rdtrob/rdt_manet_enclosure/images/2.jpg

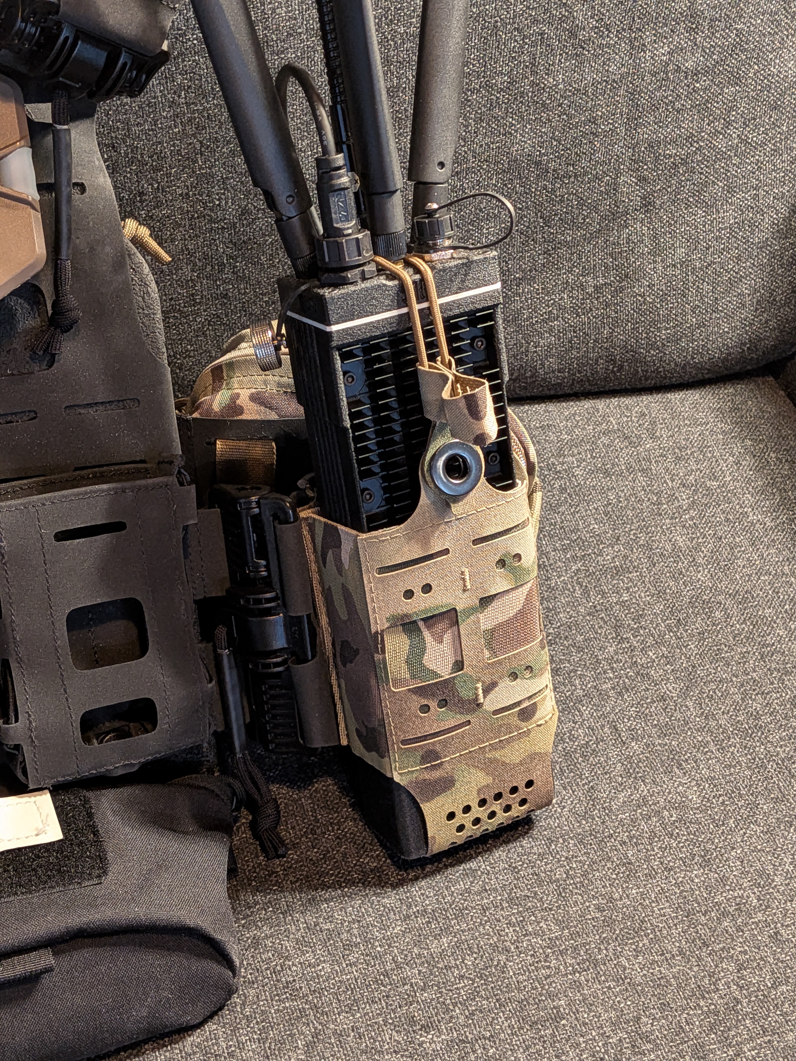
images/2.jpg
