rdtrob/rdt_manet_enclosure/images/3.jpg

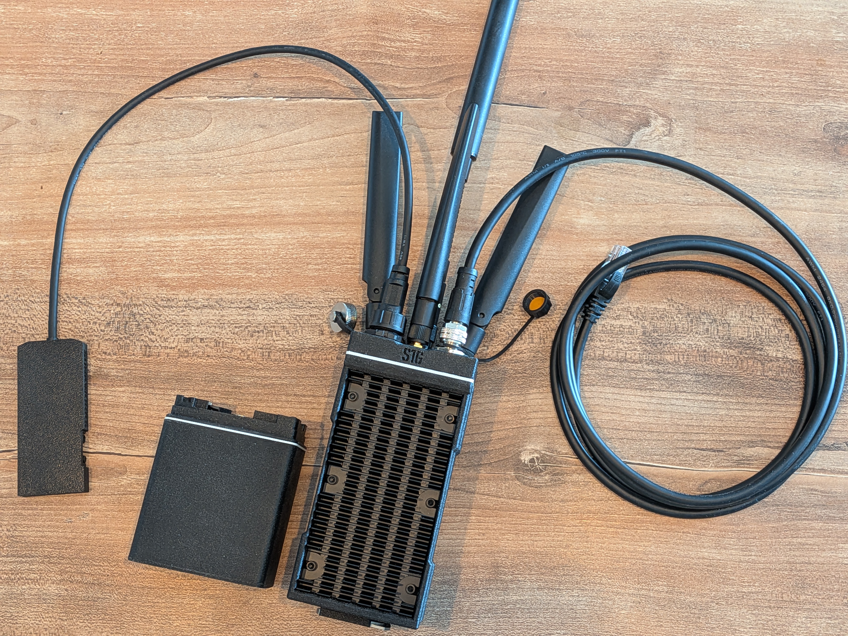
images/3.jpg
