rdtrob/rdt_manet_enclosure/images/5.jpg

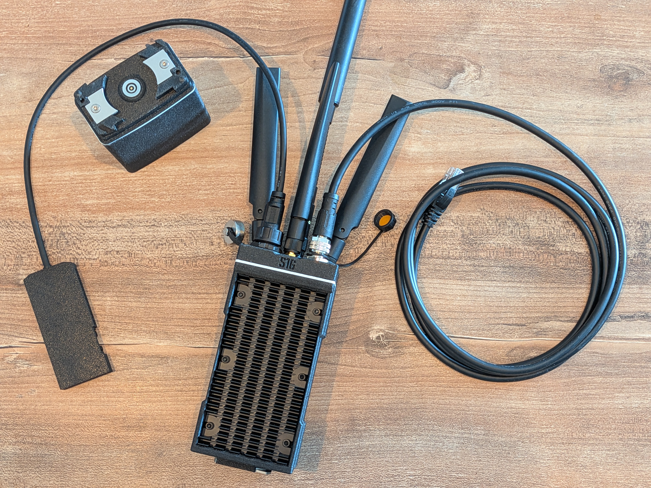
images/5.jpg
