rdtrob/rdt_manet_enclosure/images/6.jpg

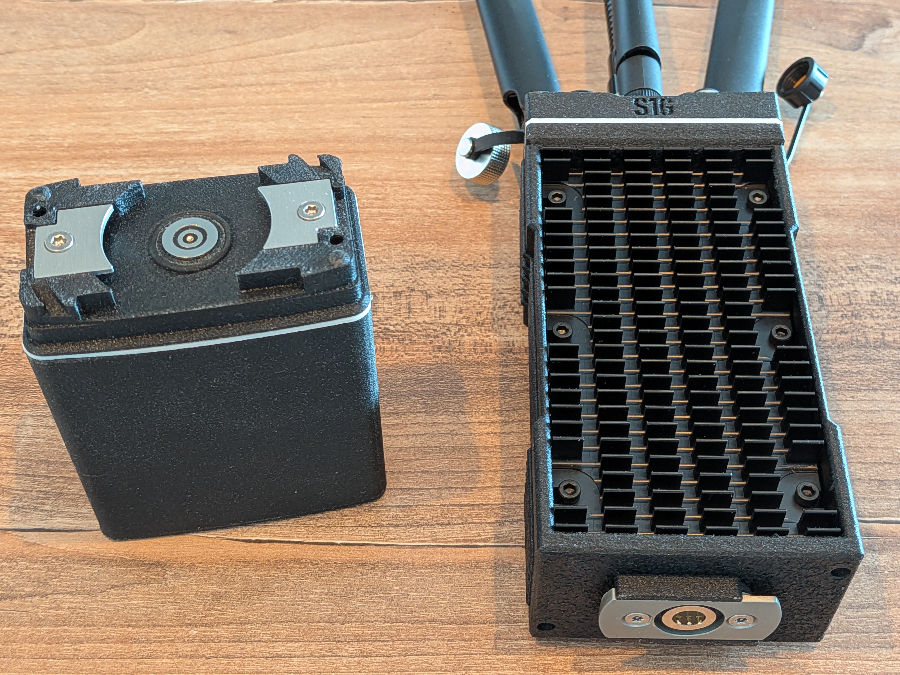
images/6.jpg
