rdtrob/rdt_manet_enclosure/images/7.jpg

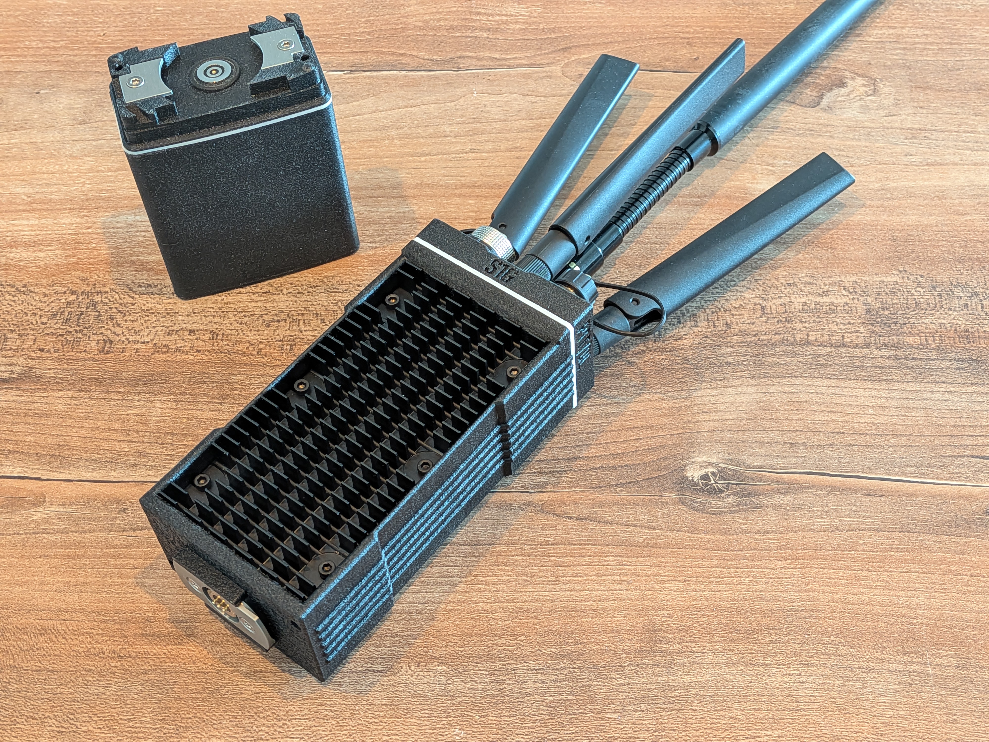
images/7.jpg
