rdtrob/rdt_manet_enclosure/images/8.jpg

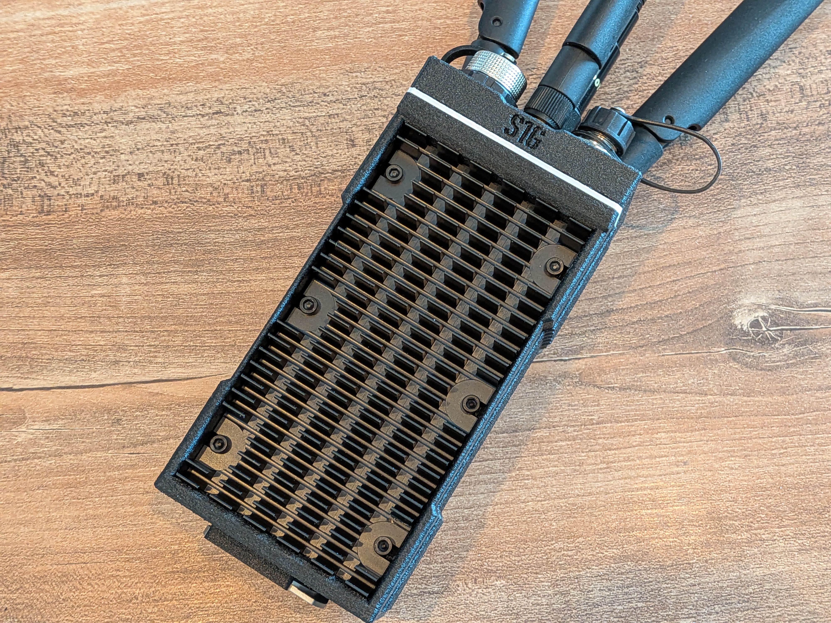
images/8.jpg
