rdtrob/rdt_manet_enclosure/images/9.jpg

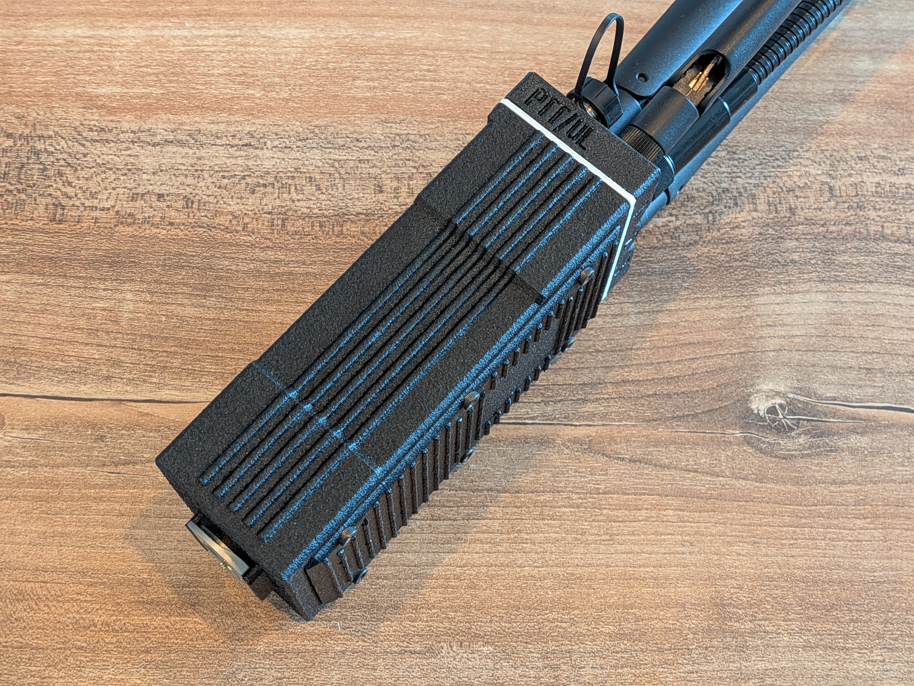
images/9.jpg
