rdtrob/rdt_manet_enclosure/images/10.jpg

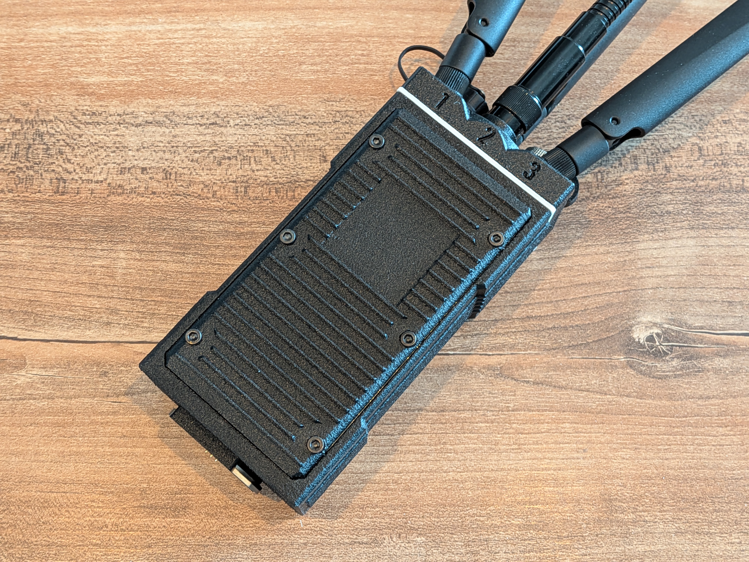
images/10.jpg
