rdtrob/rdt_manet_enclosure/images/11.jpg

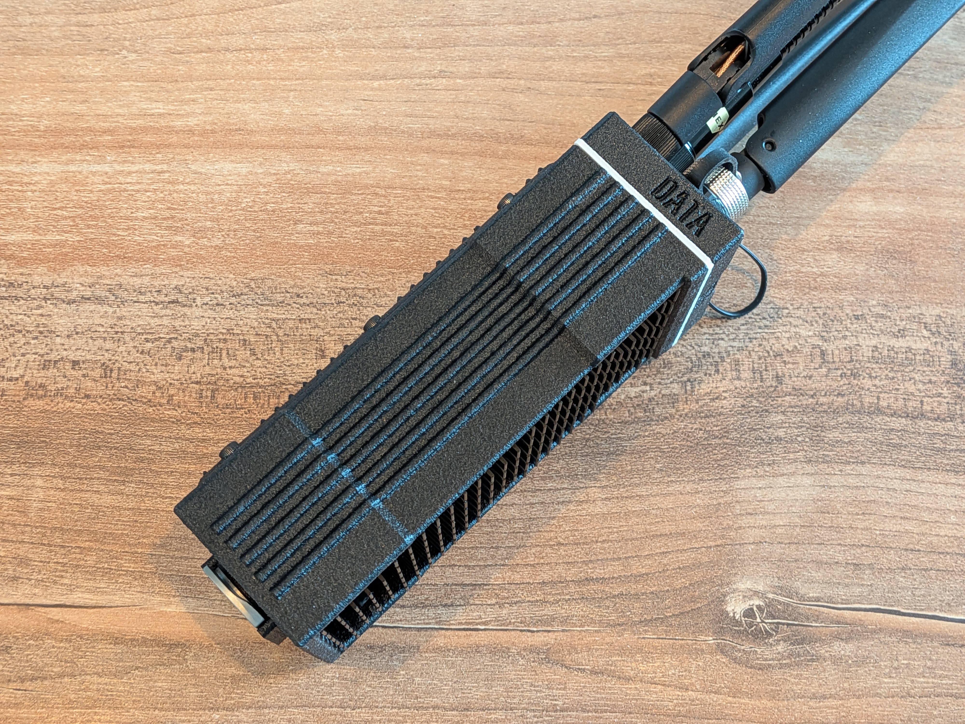
images/11.jpg
