rdtrob/rdt_manet_enclosure/images/12.jpg

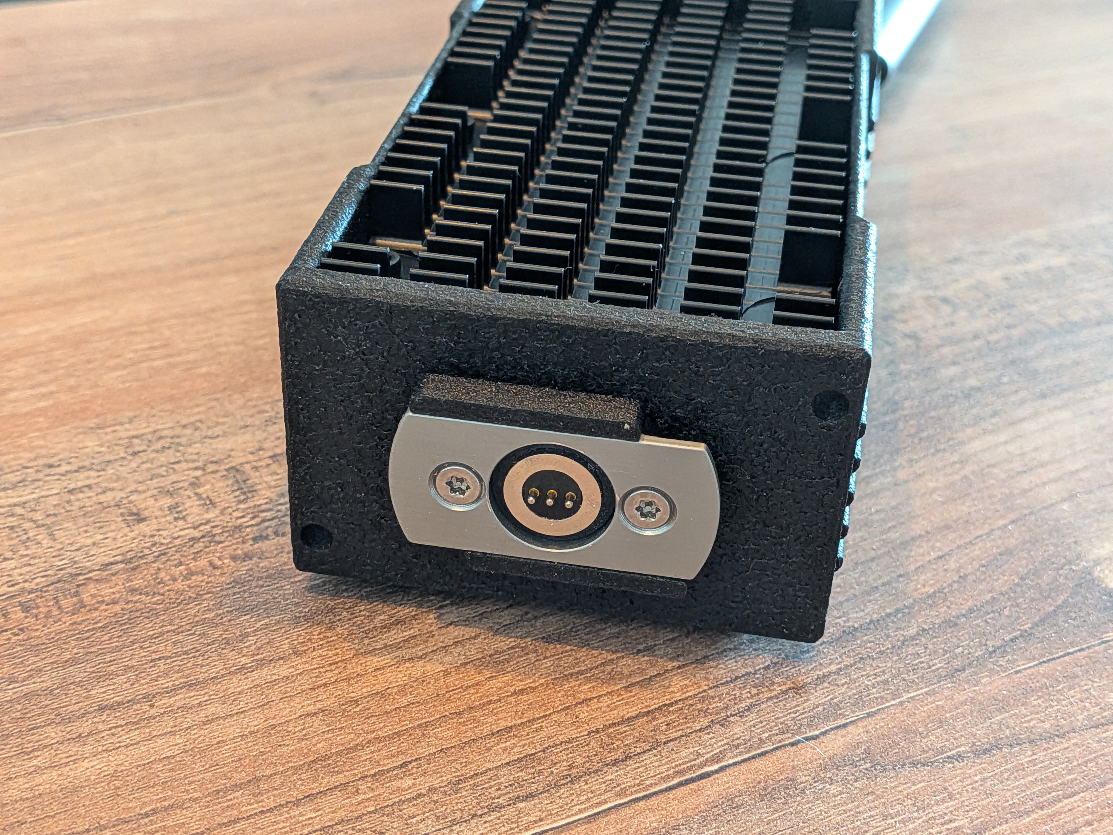
images/12.jpg
