rdtrob/rdt_manet_enclosure/images/13.jpg

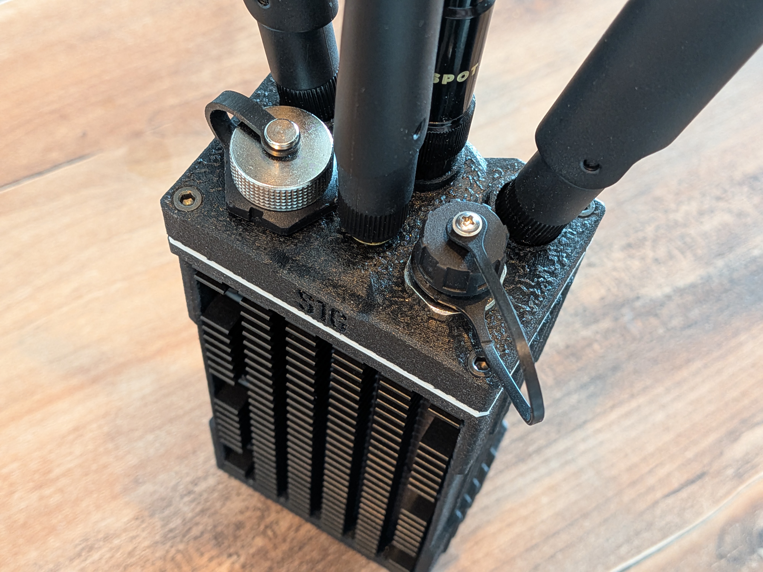
images/13.jpg
