rdtrob/rdt_manet_enclosure/images/14.jpg

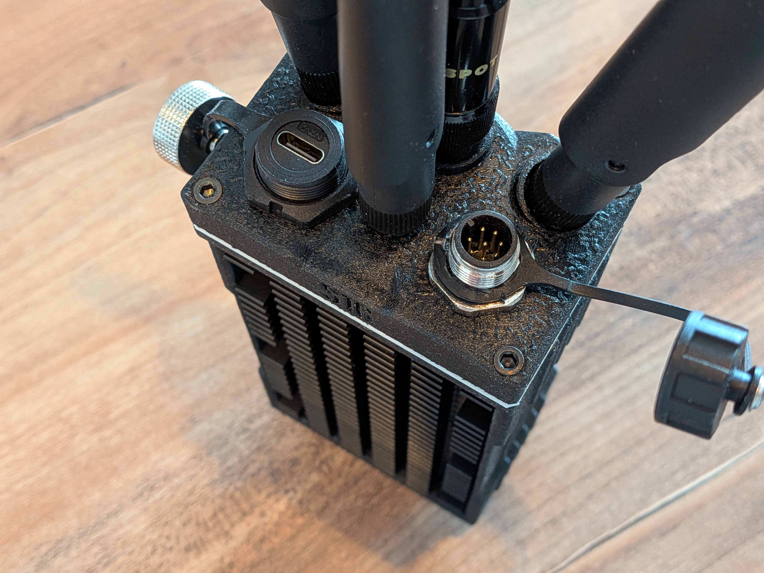
images/14.jpg
