rdtrob/rdt_manet_enclosure/images/15.jpg

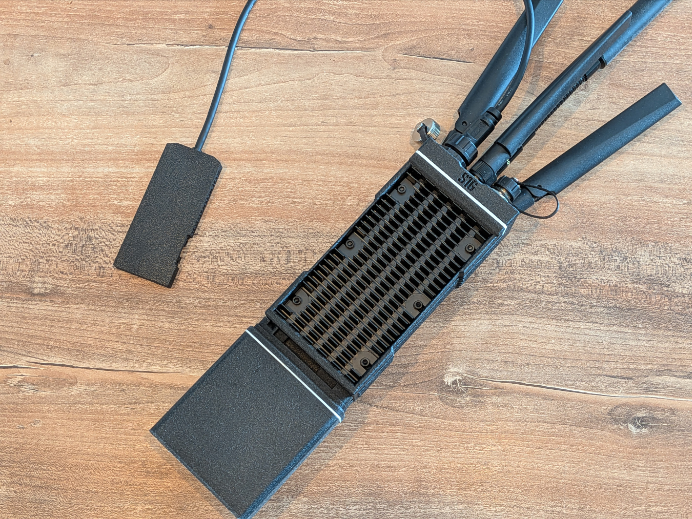
images/15.jpg
