rdtrob/rdt_manet_enclosure/images/16.jpg

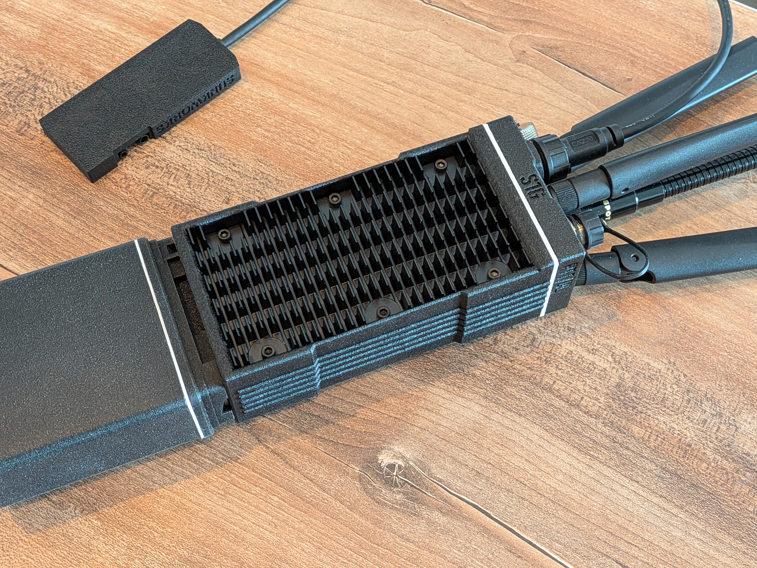
images/16.jpg
