rdtrob/rdt_manet_enclosure/images/render/render_1.png

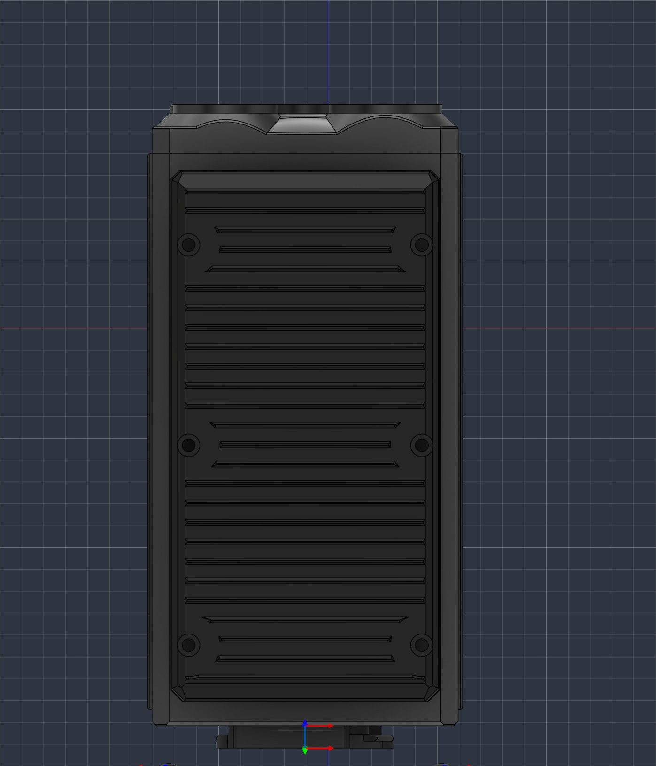
images/render/render_1.png
