rdtrob/rdt_manet_enclosure/images/render/render_2.png

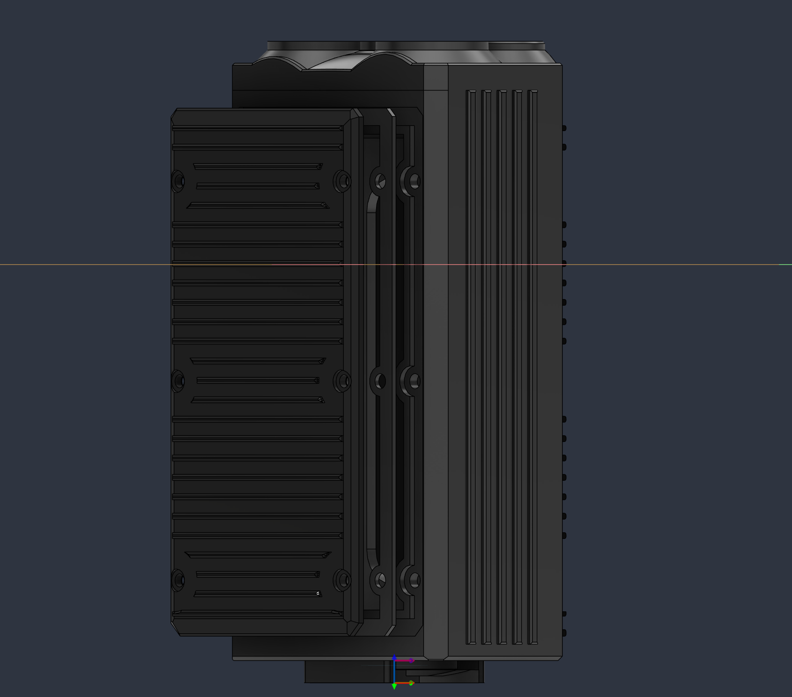
images/render/render_2.png
