rdtrob/rdt_manet_enclosure/images/render/render_3.png

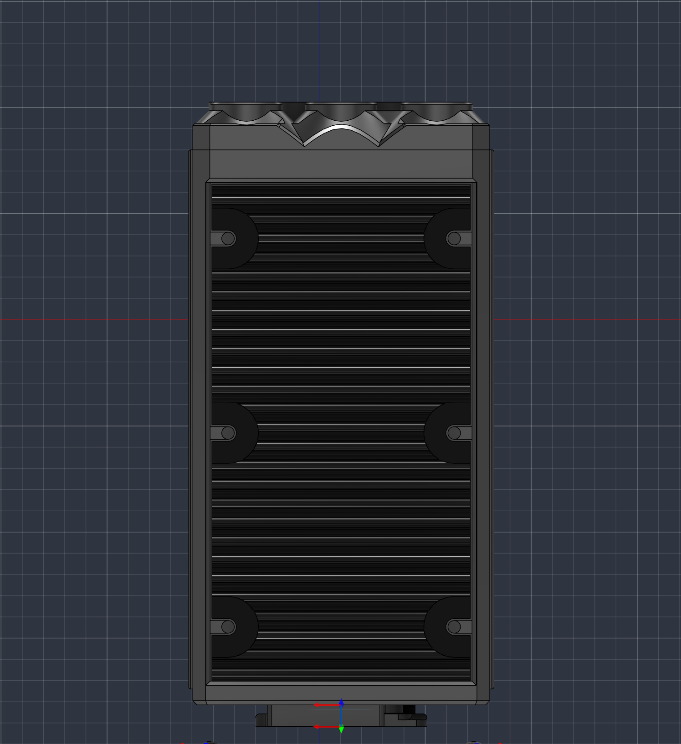
images/render/render_3.png
