rdtrob/rdt_manet_enclosure/images/render/render_5.png

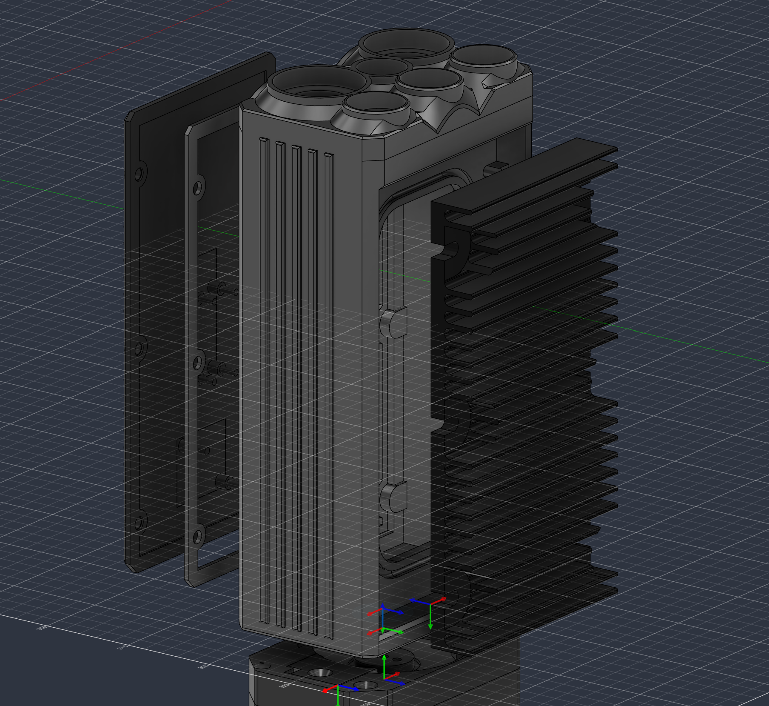
images/render/render_5.png
