rdtrob/rdt_manet_enclosure/images/components/external_USB-C_connector.png

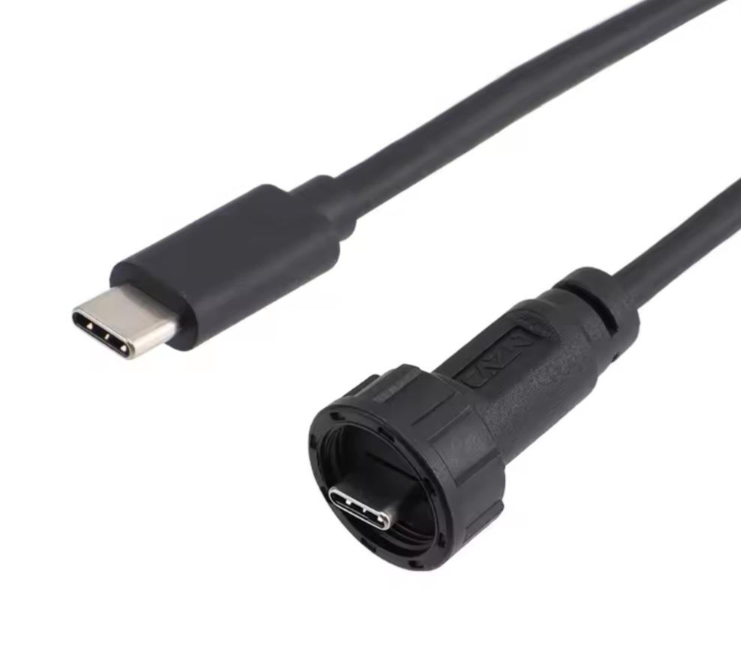
images/components/external_USB-C_connector.png
