rdtrob/rdt_manet_enclosure/images/components/flat_USB-A_to_USB-C_cable.png

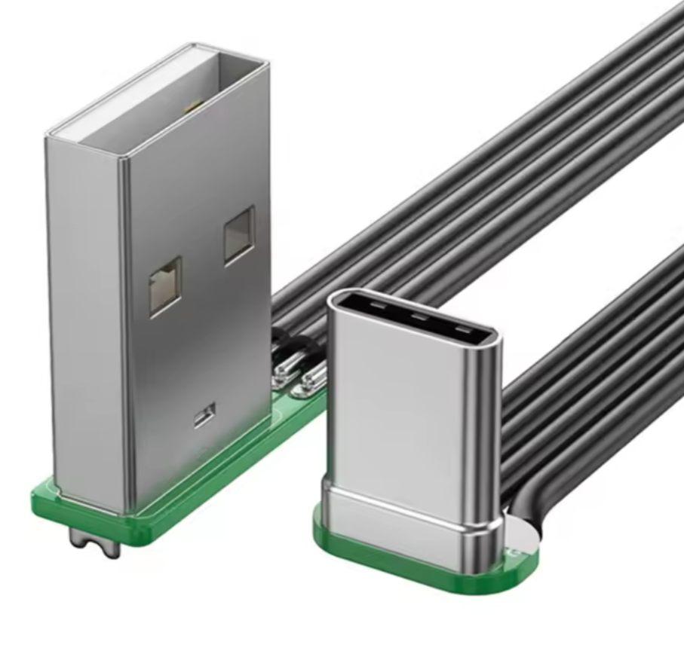
images/components/flat_USB-A_to_USB-C_cable.png
