rdtrob/rdt_manet_enclosure/images/components/Magnetic_Pogo_PIN_connector_12mm_6pin.png

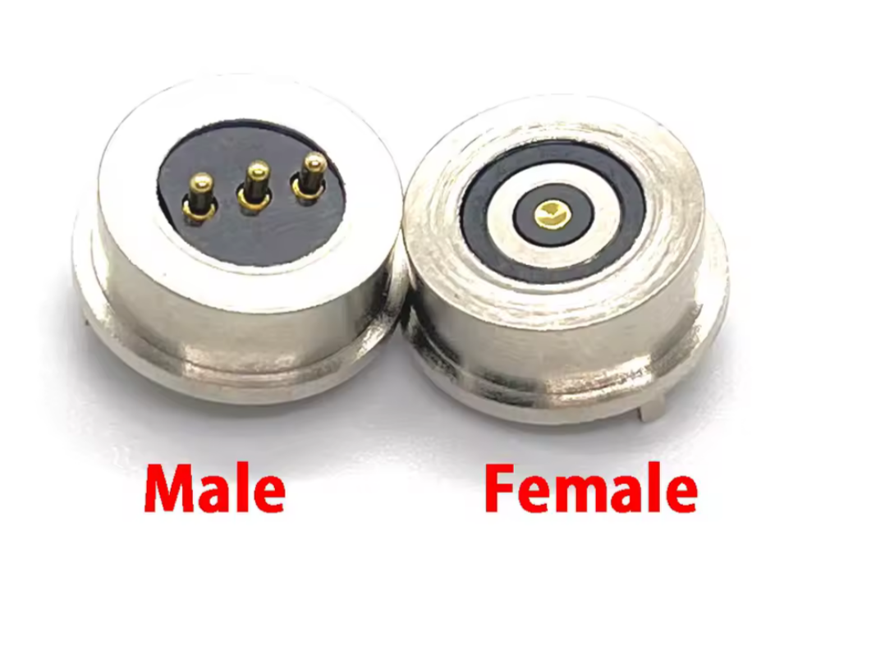
images/components/Magnetic_Pogo_PIN_connector_12mm_6pin.png
