rdtrob/rdt_manet_enclosure/images/components/pololu_buck_converter.png

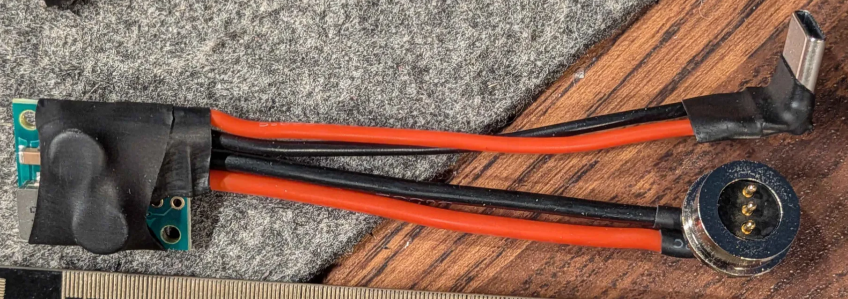
images/components/pololu_buck_converter.png
