rdtrob/rdt_manet_enclosure/images/components/USB_ribbon_cable.png

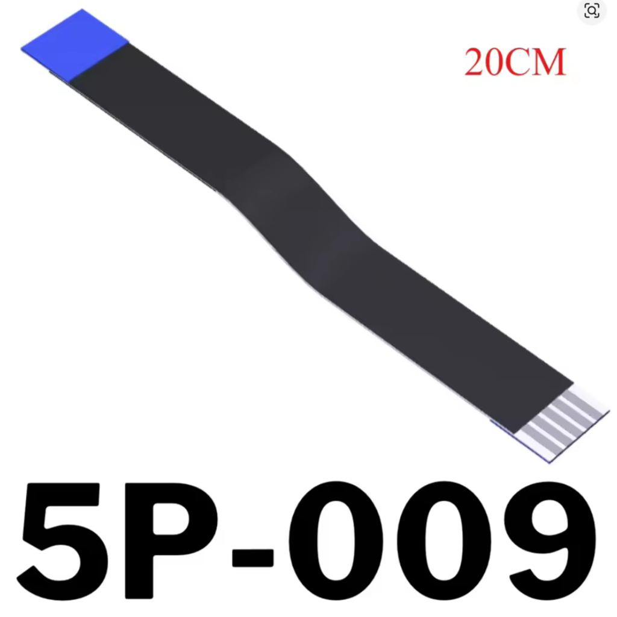
images/components/USB_ribbon_cable.png
